andersonLuizFerreira/SimulDIESEL/local-api/src/SimulDIESEL/SimulDIESEL/RESOURCES/MR.jpg

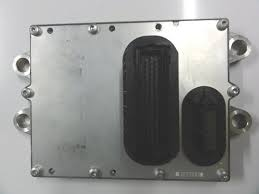
local-api/src/SimulDIESEL/SimulDIESEL/RESOURCES/MR.jpg
