andersonLuizFerreira/SimulDIESEL/local-api/src/SimulDIESEL/SimulDIESEL/RESOURCES/turn on.png

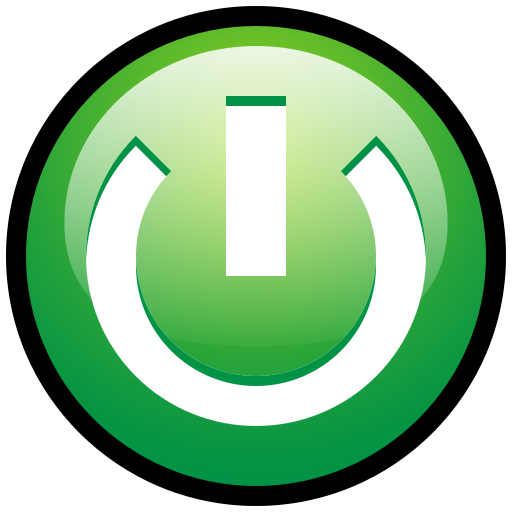
local-api/src/SimulDIESEL/SimulDIESEL/RESOURCES/turn on.png
