andersonLuizFerreira/SimulDIESEL/docs/00-INDICE.md

⬅ [Retornar para SimulDIESEL — Documentação Oficial](README.md)
⬅ [Retornar para Índice Geral](00-INDICE.md)

# Índice Geral da Navegação

Este documento é o **mapa completo clicável** da documentação oficial do SimulDIESEL.

Fora desta página, a navegação estrutural continua restrita à relação pai -> filhos imediatos.

## Acesso rápido

* [Página inicial da documentação](README.md)
* [Visão Geral do Projeto](01-visao-geral/01-visao-geral-projeto.md)
* [Organização do Repositório](09-desenvolvimento/01-organizacao-repositorio.md)

## Árvore oficial completa

- [Visão Geral do Projeto](01-visao-geral/01-visao-geral-projeto.md)
  - [Visão Arquitetural](02-arquitetura/01-visao-arquitetural.md)
    - [Visão Física do Projeto](02-arquitetura/02-visao-fisica.md)
      - [API e Host Local](02-arquitetura/04-api-e-host-local.md)
        - [Interface de Usuário](05-software-dashboard/02-interface-usuario.md)
        - [Banco Local API](02-arquitetura/12-banco-local-api.md)
        - [BLL do Host](02-arquitetura/05-bll-do-host.md)
          - [FormsLogic e Fachadas do Host](02-arquitetura/05-bll-do-host/01-formslogic-e-fachadas.md)
          - [Clients BPM, GSA e UCE](02-arquitetura/05-bll-do-host/02-clients-bpm-e-gsa.md)
        - [DAL do Host](02-arquitetura/06-dal-do-host.md)
          - [Sessão, SDH e SDGW na DAL](02-arquitetura/06-dal-do-host/01-sessao-sdh-e-sdgw.md)
          - [Framing, Scheduler e Supervisor](02-arquitetura/06-dal-do-host/02-framing-scheduler-e-supervisor.md)
        - [DTL do Host](02-arquitetura/07-dtl-do-host.md)
          - [Contratos SDH, SDGW e DTOs](02-arquitetura/07-dtl-do-host/01-contratos-sdh-e-dtos.md)
        - [Transporte do Host](02-arquitetura/08-transporte-do-host.md)
          - [SwitchableTransport e Contratos de Transporte](02-arquitetura/08-transporte-do-host/01-switchable-transport.md)
          - [Serial e Bluetooth no Host](02-arquitetura/09-serial-e-bluetooth.md)
            - [Catálogo Bluetooth e Portas no Windows](02-arquitetura/09-serial-e-bluetooth/01-catalogo-e-portas-bluetooth.md)
      - [Hardware da Bancada](02-arquitetura/10-hardware-da-bancada.md)
        - [Backplane](03-hardware/01-backplane.md)
          - [Baby Boards](03-hardware/02-baby-boards.md)
            - [Construção Física das Boards](03-hardware/05-boards-fisicas.md)
              - [GSA — Gerador de Sinais Analógicos](03-hardware/boards/03-gsa/README.md)
                - [Funcionamento Eletrônico](03-hardware/boards/03-gsa/01-funcionamento-eletronico.md)
          - [Barramentos](03-hardware/03-barramentos.md)
          - [Alimentação](03-hardware/04-alimentacao.md)
      - [Módulo em Teste e X-CONN](02-arquitetura/11-modulo-em-teste-e-xconn.md)
    - [Visão Lógica do Projeto](02-arquitetura/03-visao-logica.md)
      - [Camadas do Sistema](02-arquitetura/02-camadas-do-sistema.md)
        - [Fluxo de Comunicação](02-arquitetura/03-fluxo-de-comunicacao.md)
          - [Protocolos e Contratos](06-protocolos/README.md)
            - [Onboarding — Arquitetura de Comandos (SDH)](06-protocolos/00-onboarding-comandos.md)
              - [SDH Command Model](06-protocolos/01-sdh-command-model.md)
                - [SDH Response Model](06-protocolos/02-sdh-response-model.md)
              - [SDH Examples](06-protocolos/03-sdh-examples.md)
                - [GSA — Contrato SDH/TLV](06-protocolos/06-gsa-sdh-tlv.md)
                - [UCE — Contrato SDH/TLV](06-protocolos/07-uce-sdh-tlv.md)
            - [CAN](06-protocolos/04-can.md)
            - [J1939](06-protocolos/05-j1939.md)
      - [Arquitetura de Firmware](04-firmware/01-arquitetura-firmware.md)
        - [Drivers de Firmware](04-firmware/02-drivers.md)
        - [Gerenciamento de Recursos em Firmware](04-firmware/03-gerenciamento-recursos.md)
        - [Arquitetura SDH no Gateway](04-firmware/04-sdh-gateway-architecture.md)
          - [Catálogo de Baby Boards e Targets SDH](04-firmware/05-catalogo-baby-boards.md)
            - [Boards de Firmware](04-firmware/boards/README.md)
              - [BPM](04-firmware/boards/BPM/01-bpm.md)
              - [PSU](04-firmware/boards/PSU/02-psu.md)
              - [GSA](04-firmware/boards/GSA/03-gsa.md)
              - [UCE](04-firmware/boards/UCE/11-uce.md)
              - [GSC](04-firmware/boards/04-gsc.md)
              - [URL](04-firmware/boards/05-url.md)
              - [SLU](04-firmware/boards/06-slu.md)
              - [UCO](04-firmware/boards/07-uco.md)
              - [UCS](04-firmware/boards/08-ucs.md)
              - [UIOD](04-firmware/boards/09-uiod.md)
              - [UHM](04-firmware/boards/10-uhm.md)
          - [Tabela Mestra de Binding Lógico-Físico do Gateway](04-firmware/06-gateway-binding-logico-fisico.md)
          - [Resolver Engine do Gateway](04-firmware/07-resolver-engine-gateway.md)
      - [Arquitetura do Software Dashboard (Local API)](05-software-dashboard/01-arquitetura-software.md)
        - [Camada Hardware do Software](05-software-dashboard/03-camada-hardware.md)
          - [Arquitetura SDH no Host](05-software-dashboard/04-sdh-host-architecture.md)
            - [Handshake e Estados da Sessão](05-software-dashboard/04-sdh-host-architecture/01-handshake-e-estados-da-sessao.md)
            - [Scheduler, Retry e Supervisão do Link](05-software-dashboard/04-sdh-host-architecture/02-scheduler-retry-e-supervisao.md)
            - [Fluxo GSA do Comando ao Evento](05-software-dashboard/04-sdh-host-architecture/03-fluxo-gsa-do-comando-ao-evento.md)
            - [Parsing e Tratamento de Respostas](05-software-dashboard/04-sdh-host-architecture/04-parsing-e-tratamento-de-respostas.md)
        - [Simulação de Módulos](07-simulacoes/01-simulacao-modulos.md)
          - [Simulação de Sensores](07-simulacoes/02-simulacao-sensores.md)
          - [Simulação de Atuadores](07-simulacoes/03-simulacao-atuadores.md)
        - [Manutenção de Módulos](08-casos-de-uso/01-manutencao-modulos.md)
          - [Diagnóstico de Falhas](08-casos-de-uso/02-diagnostico.md)
            - [Testes de Bancada](08-casos-de-uso/03-testes-bancada.md)
              - [Testes de Hardware](10-testes/01-testes-hardware.md)
              - [Testes de Firmware](10-testes/02-testes-firmware.md)
              - [Testes de Integração](10-testes/03-testes-integracao.md)
- [Organização do Repositório](09-desenvolvimento/01-organizacao-repositorio.md)
  - [Padrões de Código](09-desenvolvimento/02-padroes-codigo.md)
    - [Fluxo Git](09-desenvolvimento/03-fluxo-git.md)
- [Planejamento](11-planejamento/01-planejamento.md)
  - [Próximas Funcionalidades](11-planejamento/02-proximas-funcionalidades.md)
- [Especificações](12-documentacao-tecnica/01-especificacoes.md)
  - [Diagramas](12-documentacao-tecnica/02-diagramas.md)
    - [Contratos de Software](12-documentacao-tecnica/03-contratos-software.md)

## Glossário

- **Índice geral**: única página autorizada a apontar para qualquer nó da árvore viva.
- **Ramo**: sequência de páginas pertencentes ao mesmo aprofundamento temático.
- **Pai imediato**: documento estrutural acima da página atual na árvore.
- **ONDE**: trilha física de pilha, arquivos, conectores e posição das classes.
- **COMO**: trilha lógica de função, estados, fluxo, scheduler, retry e eventos.
