andersonLuizFerreira/SimulDIESEL/docs/04-firmware/boards/06-slu.md

⬅ [Retornar para Boards de Firmware](README.md)
⬅ [Retornar para Índice Geral](../../00-INDICE.md)

# SLU

## Nome canônico

SLU

## Identificador SDH da board

SLU

## Código legado numérico no gateway

    PENDENTE DE DEFINIÇÃO OFICIAL

## Responsabilidade principal no firmware

PENDENTE DE DEFINIÇÃO OFICIAL.

## Resumo funcional

Board identificada como SLU. Descrição funcional oficial ainda pendente.

## Resources lógicos observados/aprovados

- PENDENTE DE DEFINIÇÃO OFICIAL

## Targets SDH observados/aprovados

- PENDENTE DE DEFINIÇÃO OFICIAL

## Operações SDH aplicáveis

    read
    set
    cfg
    run
    status
    reset

## Exemplos de acesso via comando SDH

    PENDENTE DE DEFINIÇÃO OFICIAL

## Observações

- O identificador SDH SLU está reservado na arquitetura.
- Os recursos internos e exemplos de comando devem ser consolidados quando o contrato da board for fechado.

## Pendências desta documentação

- Confirmar o código legado numérico da board no gateway.
- Confirmar a tabela oficial de resources internos.
- Confirmar o binding lógico-físico no firmware do gateway.

## Glossário

- **Firmware**: software embarcado executado nas boards e no gateway.
- **Gateway**: firmware central responsável por receber, rotear e responder transações.
- **TLV**: formato interno de transação baseado em Type-Length-Value.
- **Board**: unidade funcional conectada à bancada e controlada pelo gateway.
- **SDH**: SimulDiesel Hardware Command, envelope semântico de comandos do projeto.

## Próximas camadas

- Esta é uma página terminal deste ramo da documentação.
