andersonLuizFerreira/SimulDIESEL/docs/04-firmware/boards/10-uhm.md

⬅ [Retornar para Boards de Firmware](README.md)
⬅ [Retornar para Índice Geral](../../00-INDICE.md)

# UHM

## Nome canônico

UHM

## Identificador SDH da board

UHM

## Código legado numérico no gateway

    PENDENTE DE DEFINIÇÃO OFICIAL

## Responsabilidade principal no firmware

PENDENTE DE DEFINIÇÃO OFICIAL.

## Resumo funcional

Board ou entidade lógica identificada como UHM. Descrição funcional oficial ainda pendente.

## Resources lógicos observados/aprovados

- PENDENTE DE DEFINIÇÃO OFICIAL

## Targets SDH observados/aprovados

- PENDENTE DE DEFINIÇÃO OFICIAL

## Operações SDH aplicáveis

    read
    set
    cfg
    run
    status
    reset

## Exemplos de acesso via comando SDH

    PENDENTE DE DEFINIÇÃO OFICIAL

## Observações

- O identificador UHM aparece na arquitetura geral do projeto.
- Os recursos, papéis e exemplos de comandos devem ser consolidados oficialmente.

## Pendências desta documentação

- Confirmar o código legado numérico da board no gateway.
- Confirmar a tabela oficial de resources internos.
- Confirmar o binding lógico-físico no firmware do gateway.

## Glossário

- **Firmware**: software embarcado executado nas boards e no gateway.
- **Gateway**: firmware central responsável por receber, rotear e responder transações.
- **TLV**: formato interno de transação baseado em Type-Length-Value.
- **Board**: unidade funcional conectada à bancada e controlada pelo gateway.
- **SDH**: SimulDiesel Hardware Command, envelope semântico de comandos do projeto.

## Próximas camadas

- Esta é uma página terminal deste ramo da documentação.
