andersonLuizFerreira/SimulDIESEL/.agents/skills/firmware-uce/SKILL.md

# Nome

Firmware UCE

## Objetivo

Orientar ETAPAS do firmware UCE, SPI slave, LedService, CanService, SDCTP embarcado, driver CAN e execucao fisica.

## Quando usar

Use para firmware da UCE, servicos CAN/LED, SPI, IRQ, tabelas RX/TX, driver CAN e contratos TLV da UCE.

## Quando nao usar

Nao use para alterar UI/API/banco sem pedido ponta a ponta.

## Escopo permitido

- `hardware/firmware/UCE - Unidade de comunicacao externa/`
- documentos e dumps de UCE.

## Escopo proibido

- Alterar BPM/host para mascarar problema da UCE sem autorizacao.
- Mudar pinagem ou TLVs consolidados sem congelamento.

## Arquivos/pastas provaveis

- `src/main.cpp`
- `include/config.h`
- `include/defs.h`
- `lib/core/transport/`
- `lib/core/services/`
- `lib/services/can/`
- `lib/services/led/`

## Padroes do projeto

- UCE e board remota por SPI.
- Executa LED e CAN fisico.
- CAN atual agrega controle e massa em `CanService`, com wrappers SDCTP.
- Eventos sobem para BPM por IRQ/event queue.

## Checklist de validacao

- [ ] `platformio run` em UCE quando houver codigo.
- [ ] Contratos TLV preservados.
- [ ] Pinos SPI/IRQ/reset preservados.
- [ ] Build host/BPM apenas se a ETAPA tocar contrato ponta a ponta.

## Checklist de entrega

- [ ] Servicos alterados.
- [ ] TLVs impactados.
- [ ] Resultado PlatformIO.
- [ ] Validacao de bancada, se executada.

## Riscos comuns

- Quebrar SPI nativo do Due.
- Misturar controle CAN e massa sem documentar.
- Remover fakes/legados sem decisao.

## Regras de nao regressao

- UCE continua executora fisica.
- SDGW nao entra na logica interna da UCE alem do contrato recebido via BPM.
- SDCTP preserva RX/TX validado.
