andersonLuizFerreira/SimulDIESEL/out/dumps/relatorio_task/ETAPA_002_relatorio_consolidacao_documental.md

# ETAPA_002 - Relatorio de consolidacao documental

## Escopo executado

Consolidacao estrutural de `docs/` conforme `.agents/task-execution-workflow/ETAPA_002_consolidacao_estrutura_docs.md`.

Nao foram alterados firmware, codigo-fonte funcional, banco, UI ou contratos SDH/SDGW/SDCTP.

## Resultado estrutural

A arvore viva de `docs/` foi consolidada diretamente na raiz:

```text
docs/
|-- README.md
|-- 00-INDICE.md
|-- 01-visao-geral/
|-- 02-arquitetura/
|-- 03-hardware/
|-- 04-firmware/
|-- 05-software-dashboard/
|-- 06-protocolos/
|-- 07-simulacoes/
|-- 08-casos-de-uso/
|-- 09-desenvolvimento/
|-- 10-testes/
|-- 11-planejamento/
`-- 12-documentacao-tecnica/
```

`docs/` ficou com 84 arquivos Markdown na arvore viva.

## Movimentos e remocoes

- `docs/official/*` foi absorvido para `docs/*`.
- `docs/legacy/` foi removido da arvore viva e preservado em `out/dumps/docs_legacy_2026-05-18/`.
- `docs/architecture/` foi removido da arvore viva e preservado em `out/dumps/relatorio_task/ETAPA_002_architecture_parallel_archive/`.
- `docs/ETAPA_10_SDCTP_CAN_TRANSPORT_PROTOCOL.md` foi removido da arvore viva e preservado em `out/dumps/relatorio_task/ETAPA_002_ETAPA_10_SDCTP_CAN_TRANSPORT_PROTOCOL_archive.md`.
- `docs/DOCUMENTATION_RULES.md` foi removido apos absorcao das regras relevantes em `.agents/skills/docs-governance/SKILL.md`.
- `docs/.gitkeep` foi removido por nao ser mais necessario.

## Conteudo util absorvido

- A arvore oficial baseada em `docs/official/` foi promovida para a raiz viva.
- Regras de navegacao, indice geral, glossario, nomenclatura `SDGW (SimulDiesel GateWay)`, separacao `ONDE`/`COMO` e estados documentais permanecem governadas por `.agents/README.md` e `.agents/skills/docs-governance/SKILL.md`.
- O indice geral passou a apontar para caminhos sem `official/`.
- Paginas UCE e Banco Local API foram expostas no indice geral.

## Conflitos e redundancias

- `docs/official/` era redundante com a raiz viva desejada.
- `docs/legacy/` era fonte historica paralela dentro de `docs/`; foi preservada fora da arvore viva.
- `docs/architecture/` continha contrato arquitetural paralelo; foi preservado fora da arvore viva para consulta e eventual absorcao futura.
- `docs/DOCUMENTATION_RULES.md` duplicava regras de governanca que agora pertencem a `.agents/`.

## Destino final proposto para legado

Destino aplicado nesta ETAPA:

```text
out/dumps/docs_legacy_2026-05-18/
```

Esse destino preserva o historico fora da documentacao viva. O rollback permanece disponivel via Git.

## Validacoes executadas

- Coerencia com `.agents/README.md`: OK.
- Coerencia com `.agents/skills/docs-governance/SKILL.md`: OK apos atualizacao da arvore autorizada.
- Ausencia de governanca documental paralela dentro de `docs/`: OK; `DOCUMENTATION_RULES.md` foi removido.
- Preservacao de conteudo util: OK; conteudo paralelo foi movido para `out/dumps/` ou absorvido.
- Navegacao documental basica: OK; verificador de links Markdown relativos retornou `broken_links=0`.
- Build funcional: NAO APLICAVEL por ETAPA exclusivamente documental.

## Pendencias

- Revisao humana pode decidir se o material preservado em `out/dumps/docs_legacy_2026-05-18/` deve permanecer versionado, ser compactado ou removido em ETAPA futura.
- O arquivo preservado de contratos arquiteturais em `out/dumps/relatorio_task/ETAPA_002_architecture_parallel_archive/` pode ser avaliado em ETAPA futura para absorcao seletiva em `docs/12-documentacao-tecnica/`.

## Rollback

Rollback preservado via Git. Nenhum arquivo funcional foi alterado.
