andersonLuizFerreira/SimulDIESEL/.agents/task-execution-workflow/ETAPA_002_consolidacao_estrutura_docs.md

# ETAPA_002_consolidacao_estrutura_docs

## STATUS

CONCLUIDA

## CRIADA_POR

Humano + ChatGPT

## EXECUTADA_POR

Codex

## VALIDADA_POR

pendente de confirmacao

## DATA_CRIACAO

2026-05-18

## DATA_EXECUCAO

2026-05-18

## DATA_VALIDACAO

pendente de confirmacao

## Objetivo

Consolidar a estrutura oficial de `docs/` utilizando como base a arvore atualmente existente em `docs/official/`, eliminando estruturas documentais paralelas e alinhando a documentacao com a nova governanca documental.

## Escopo permitido

- Auditar `docs/official/`.
- Absorver `docs/official/` para a raiz viva de `docs/`.
- Atualizar `00-INDICE.md`.
- Atualizar `README.md` de `docs/`.
- Atualizar `.agents/skills/docs-governance/SKILL.md`.
- Identificar redundancias documentais.
- Consolidar conteudo util.
- Remover `DOCUMENTATION_RULES.md` apos validacao de absorcao.
- Identificar estruturas paralelas restantes.
- Propor saneamento final da estrutura documental.

## Fora de escopo

- Alterar firmware.
- Alterar codigo-fonte funcional.
- Escolher autonomamente docs -> codigo ou codigo -> docs.
- Saneamento automatico de divergencias funcionais.
- Alterar contratos SDH/SDGW/SDCTP.

## Regras aplicaveis

- `.agents/README.md`
- `.agents/skills/task-execution-workflow/SKILL.md`
- `.agents/skills/docs-governance/SKILL.md`

## Decisoes humanas consolidadas

- A estrutura oficial viva de `docs/` deve ser baseada na estrutura atualmente existente em `docs/official/`.
- `docs/official/` nao deve permanecer como raiz paralela.
- `docs/legacy/` nao deve permanecer como estrutura viva.
- `DOCUMENTATION_RULES.md` deve ser removido apos absorcao completa das regras relevantes.
- Na raiz de `docs/` devem existir apenas:

```text
docs/
|-- README.md
|-- 00-INDICE.md
|-- <pastas associadas>
```

## Tarefas

- [x] OK - Auditar estrutura atual de `docs/official/`.
- [x] OK - Definir arvore final proposta para `docs/`.
- [x] OK - Identificar conflitos de nomenclatura.
- [x] OK - Identificar redundancias entre `docs/`, `docs/official/` e `docs/legacy/`.
- [x] OK - Consolidar conteudo util antes de mover/remover documentos.
- [x] OK - Atualizar `.agents/skills/docs-governance/SKILL.md` com a nova arvore oficial.
- [x] OK - Atualizar `00-INDICE.md` para refletir a nova estrutura.
- [x] OK - Atualizar `docs/README.md`.
- [x] OK - Remover `DOCUMENTATION_RULES.md` apos validacao de absorcao.
- [x] OK - Propor destino final para `docs/legacy/`.
- [x] OK - Verificar links internos basicos.
- [x] OK - Gerar relatorio de consolidacao documental.

## Validacao obrigatoria

- Verificar coerencia com `.agents/README.md`.
- Verificar coerencia com `.agents/skills/docs-governance/SKILL.md`.
- Verificar ausencia de governanca documental paralela.
- Verificar preservacao de conteudo util.
- Verificar navegacao documental basica.

## Entrega esperada

- Estrutura documental consolidada.
- Estrutura paralela removida ou classificada.
- `DOCUMENTATION_RULES.md` absorvido/removido.
- Relatorio de consolidacao documental.
- Atualizacao das skills/documentacao impactadas.

## Restricoes

- Nao remover conteudo util sem absorcao.
- Nao sobrescrever historico util sem consolidacao.
- Nao decidir autonomamente conflitos docs x codigo.
- Nao alterar governanca global sem autorizacao humana.

## Resultado da execucao

Execucao concluida em 2026-05-18.

Arquivos e estruturas alteradas:

- `.agents/skills/docs-governance/SKILL.md`
- `.agents/task-execution-workflow/ETAPA_002_consolidacao_estrutura_docs.md`
- `docs/README.md`
- `docs/00-INDICE.md`
- `docs/01-visao-geral/`
- `docs/02-arquitetura/`
- `docs/03-hardware/`
- `docs/04-firmware/`
- `docs/05-software-dashboard/`
- `docs/06-protocolos/`
- `docs/07-simulacoes/`
- `docs/08-casos-de-uso/`
- `docs/09-desenvolvimento/`
- `docs/10-testes/`
- `docs/11-planejamento/`
- `docs/12-documentacao-tecnica/`
- `out/dumps/docs_legacy_2026-05-18/`
- `out/dumps/relatorio_task/ETAPA_002_relatorio_consolidacao_documental.md`
- `out/dumps/relatorio_task/ETAPA_002_architecture_parallel_archive/`
- `out/dumps/relatorio_task/ETAPA_002_ETAPA_10_SDCTP_CAN_TRANSPORT_PROTOCOL_archive.md`

Arquivos e estruturas removidas da arvore viva:

- `docs/official/`
- `docs/legacy/`
- `docs/architecture/`
- `docs/DOCUMENTATION_RULES.md`
- `docs/ETAPA_10_SDCTP_CAN_TRANSPORT_PROTOCOL.md`
- `docs/.gitkeep`

Resumo:

- A arvore de `docs/official/` foi absorvida para a raiz viva de `docs/`.
- A skill `docs-governance` passou a registrar a nova arvore oficial.
- `docs/README.md` e `docs/00-INDICE.md` foram atualizados para a nova estrutura.
- `DOCUMENTATION_RULES.md` foi removido apos absorcao das regras relevantes em `.agents/`.
- O acervo legado e materiais paralelos foram preservados fora da arvore viva em `out/dumps/`.

Validacoes executadas:

- Coerencia com `.agents/README.md`: OK.
- Coerencia com `.agents/skills/docs-governance/SKILL.md`: OK.
- Ausencia de governanca documental paralela em `docs/`: OK.
- Preservacao de conteudo util: OK, via absorcao ou movimentacao para `out/dumps/`.
- Navegacao documental basica: OK, `broken_links=0`.
- Build funcional: NAO APLICAVEL por ETAPA exclusivamente documental.

Warnings e pendencias:

- Avaliar em ETAPA futura se o acervo preservado em `out/dumps/docs_legacy_2026-05-18/` deve permanecer versionado, ser compactado ou removido.
- Avaliar em ETAPA futura se o contrato preservado em `out/dumps/relatorio_task/ETAPA_002_architecture_parallel_archive/` deve ser absorvido seletivamente em `docs/12-documentacao-tecnica/`.

Rollback:

- Preservado via Git. Nenhum arquivo funcional foi alterado.

Commit hash:

- `b830a110` - Consolidate documentation structure.
