andersonLuizFerreira/SimulDIESEL/docs/06-protocolos/02-sdh-response-model.md

⬅ [Retornar para SDH Command Model](01-sdh-command-model.md)
⬅ [Retornar para Índice Geral](../00-INDICE.md)

# SDH Response Model

## Envelope de resposta

Toda resposta segue:

    version
    ok
    target
    op
    code
    message
    data
    meta

## Forma textual

Sucesso:

    sdh/1 ok <target> <op> code=OK message="..."

Erro:

    sdh/1 err <target> <op> code=INVALID_ARG message="..."

## Forma JSON

    {
      "version": "sdh/1",
      "ok": true,
      "target": "GSA.channel.status",
      "op": "get",
      "code": "OK",
      "message": "Status do canal lido",
      "data": {
        "channel": 6,
        "setpoint": 128,
        "vout": 134,
        "iread": 17,
        "enabled": true,
        "fault": false
      },
      "meta": {}
    }

## Códigos de erro

    OK
    INVALID_TARGET
    INVALID_OP
    INVALID_ARG
    MISSING_ARG
    OUT_OF_RANGE
    UNSUPPORTED
    BUSY
    FAULT
    TIMEOUT

## Tipos

- confirmação;
- leitura;
- status;
- erro.

## Referências

- `docs/06-protocolos/01-sdh-command-model.md`
- `docs/06-protocolos/03-sdh-examples.md`
- `docs/06-protocolos/06-gsa-sdh-tlv.md`

## Glossário

- **Protocolo**: conjunto de regras de formato e interpretação para comunicação.
- **Target**: identificador lógico do recurso de destino de um comando SDH.
- **Envelope**: estrutura externa que organiza os campos semânticos do comando ou resposta.
- **TLV**: contrato interno usado entre gateway e devices quando aplicável.
- **SDH**: SimulDiesel Hardware Command, envelope semântico de comandos do projeto.

## Próximas camadas

- [SDH Examples](03-sdh-examples.md)
