andersonLuizFerreira/SimulDIESEL/out/dumps/etapa_j1939_catalog_web_captured_data.md

# Dump - Dados captados na web para catalogos J1939/81

Data: 2026-05-13

## Objetivo

Registrar a lista dos dados publicos captados na web e materializados nos JSONs locais da ETAPA `Popular Catalogos J1939/81`.

Este dump documenta somente os dados versionados nos arquivos:

- `Data/Protocols/J1939/catalogs/j1939_industry_groups.json`
- `Data/Protocols/J1939/catalogs/j1939_manufacturers.json`
- `Data/Protocols/J1939/catalogs/j1939_functions.json`
- `Data/Protocols/J1939/catalogs/j1939_preferred_addresses.json`
- `Data/Protocols/J1939/catalogs/j1939_name_field_definitions.json`
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
