andersonLuizFerreira/SimulDIESEL/local-api/src/SimulDIESEL/SimulDIESEL/RESOURCES/Conectado.png

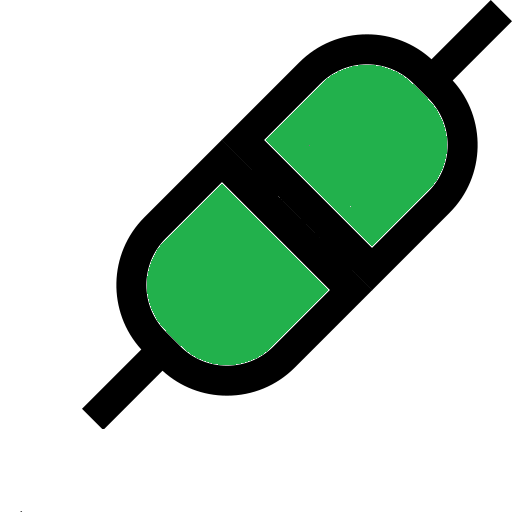
local-api/src/SimulDIESEL/SimulDIESEL/RESOURCES/Conectado.png
