andersonLuizFerreira/SimulDIESEL/tests/Leitura de alarmes/3 - somente motor.md

# Sessao
Id: a27e9f25895c4c3584975347c92bfa00
Inicio: 2026-05-14 16:29:08.665
Fim: 2026-05-14 16:29:37.622
DuracaoMs: 28956
FramesRecebidos: 2546
FramesUnicos: 2388
EventosExportados: 2543

# Resumo por PGN
- PGN=0x00F004 eventos=1098 frames=1251
- PGN=0x00F003 eventos=443 frames=443
- PGN=0x00FF1C eventos=443 frames=443
- PGN=0x00FEF2 eventos=221 frames=221
- PGN=0x00FEDF eventos=86 frames=86
- PGN=0x00FEEF eventos=44 frames=44
- PGN=0x00FEF6 eventos=44 frames=44
- PGN=0x00FF1D eventos=44 frames=44
- PGN=0x00DA00 eventos=26 frames=31
- PGN=0x00FEF7 eventos=22 frames=22
- PGN=0x00FEE4 eventos=22 frames=22
- PGN=0x00FEBD eventos=22 frames=22
- PGN=0x00FECA eventos=21 frames=21
- PGN=0x00FEE3 eventos=3 frames=3
- PGN=0x00FEFF eventos=2 frames=2
- PGN=0x00EA00 eventos=1 frames=1
- PGN=0x00EE00 eventos=1 frames=1

# Resumo por Source Address
- SA=0x00 eventos=2516 frames=2669
- SA=0xF9 eventos=26 frames=31
- SA=0xFE eventos=1 frames=1

# Address Claims detectados
- 2026-05-14 16:29:12.092 SA=0x00 NAME=8000000001570F1A RawCanId=0x18EEFF00

# Periodicidade detectada
- 2026-05-14 16:29:11.940 SA=0xF9 DST=GLOBAL PGN=0x00DA00 intervalo_ms=1013 repeticoes=4
- 2026-05-14 16:29:37.291 SA=0xF9 DST=GLOBAL PGN=0x00DA00 intervalo_ms=1013 repeticoes=3
- 2026-05-14 16:29:12.409 SA=0x00 DST=GLOBAL PGN=0x00F004 intervalo_ms=20 repeticoes=2
- 2026-05-14 16:29:12.509 SA=0x00 DST=GLOBAL PGN=0x00F004 intervalo_ms=19 repeticoes=2
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
Repeticoes: 1
Notas: Transicao detectada por mudanca de PGN, payload.

[2026-05-14 16:29:18.209]
DeltaMs: 18
Origem: 0x00
Destino: GLOBAL
RawCanId: 0x0CF00400
PGN: 0x00F004
Dados: F8 7D 7D 00 00 00 FF FF
Evento: TRANSITION
Repeticoes: 1
Notas: Transicao detectada por mudanca de PGN, payload.
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
