andersonLuizFerreira/SimulDIESEL/hardware/firmware/UCE - Unidade de comunicacao externa/include/defs.h

#pragma once
#include <stdint.h>

#define TLV_MAX_LEN               32
#define SPI_V1_MAX_FRAME_LEN      256              // [COMMISSIONING_SPI_V1]
#define SPI_V1_MAX_ENCODED_LEN    260              // [COMMISSIONING_SPI_V1]
#define SPI_V1_MAX_MSG_VALUE_LEN  (TLV_MAX_LEN - 4) // [COMMISSIONING_SPI_V1]
#define UCE_CAN_MAX_MAILBOXES     8
#define UCE_CAN_MAX_FILTERS       8
#define MAX_CAN_RX_ROWS           100
#define MAX_CAN_TX_ROWS           100

#define CAN_BITRATE_5_KBPS        0x00
#define CAN_BITRATE_10_KBPS       0x01
#define CAN_BITRATE_25_KBPS       0x02
#define CAN_BITRATE_50_KBPS       0x03
#define CAN_BITRATE_125_KBPS      0x04
#define CAN_BITRATE_250_KBPS      0x05
#define CAN_BITRATE_500_KBPS      0x06
#define CAN_BITRATE_800_KBPS      0x07
#define CAN_BITRATE_1000_KBPS     0x08

#define UCE_PIN_NOT_CONNECTED     0xFF

// ============================================================
// SPI - BPM backplane
// ============================================================
#define UCE_SPI_CS_PIN            10
#define UCE_SPI_IRQ_PIN           2
#define UCE_SPI_IRQ_ACTIVE_LEVEL  LOW
#define UCE_SPI_IRQ_IDLE_LEVEL    HIGH

#define CMD_LED_BUILTIN           0x12
#define CMD_LED_EVENT             0x13
#define CMD_CAN_CONFIG            0x20
#define CMD_CAN_ENABLE            0x21
#define CMD_CAN_STATUS            0x22
#define CMD_CAN_RESET             0x23
#define CMD_CAN_RX_POLL           0x24
#define CMD_CAN_DRIVER_LOG_POLL   0x25
#define CMD_CAN_TX                0x26
#define CMD_CAN_TX_STOP           0x27
#define CMD_CAN_RX_EVENT          0x28
#define CMD_CAN_TX_DIRECT         0x50
#define CMD_CAN_TX_CREATE         0x51
#define CMD_CAN_TX_EDIT           0x52
#define CMD_CAN_TX_DELETE         0x53
#define CMD_CAN_READ_ALL          0x43
#define CMD_CAN_ROW               0x44
#define CMD_CAN_READ_ALL_DONE     0x45
#define CMD_CAN_TIC               0x46
#define CMD_CAN_CREATE            0x40
#define CMD_CAN_EDIT              0x41
#define CMD_CAN_DELETE            0x42
#define CMD_TRANSPORT_DIAG        0x7E
#define CMD_FUNCTIONAL_ERROR      0x7F

#define UCE_TRANSPORT_DIAG_DISPATCHER_FIFO_OVERFLOW 0x01
#define UCE_TRANSPORT_DIAG_DISPATCHER_FIFO_OVERFLOW_LEN 0x07

#define UCE_ERROR_INVALID_STATE          0x03
#define UCE_ERROR_COMMAND_NOT_SUPPORTED  0x07
#define UCE_ERROR_INVALID_PAYLOAD        0x08
#define UCE_ERROR_INVALID_TLV_CRC        0x09

#define UCE_TRANSPORT_ERR_NONE          0x00
#define UCE_TRANSPORT_ERR_PRELOAD_FAIL  0x01
#define UCE_TRANSPORT_ERR_TX_UNDERRUN   0x02
#define UCE_TRANSPORT_ERR_RX_OVERFLOW   0x03
#define UCE_TRANSPORT_ERR_CLOCK_FAST    0x04
#define UCE_TRANSPORT_ERR_SESSION_ABORT 0x05

#define LED_PIN                   LED_BUILTIN
