andersonLuizFerreira/SimulDIESEL/hardware/firmware/GSA - Gerador de sinais analógicos/include/SoftwareWire.h

#pragma once

// Forwarder local para estabilizar a resolução do include do SoftwareWire
// no build do firmware da GSA. A implementação continua vindo da
// dependência usada pelo projeto.
#include "..\..\..\..\tools\GSA_Teste\.pio\libdeps\nanoatmega328\SoftwareWire\SoftwareWire.h"
